Akulkute/MINE-GUARD/Images/WhatsApp Image 2026-06-03 at 1.49.41 AM.jpeg

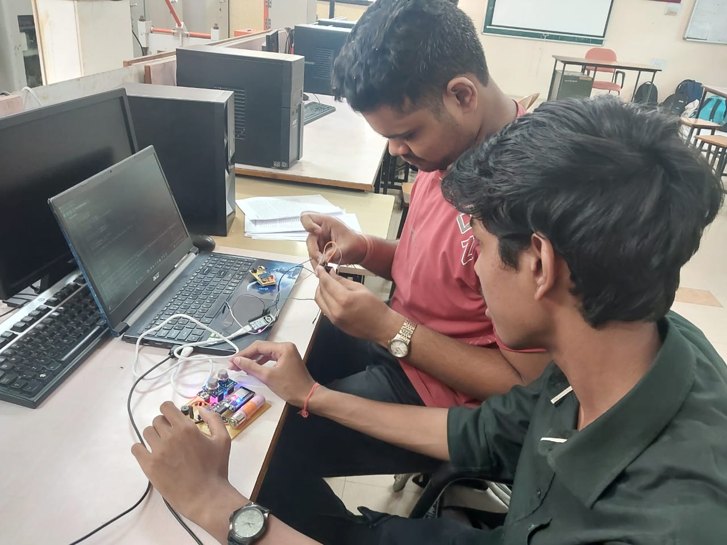
Images/WhatsApp Image 2026-06-03 at 1.49.41 AM.jpeg
