Akulkute/MINE-GUARD/PCB-files/Images/WhatsApp Image 2026-06-03 at 1.44.29 AM.jpeg

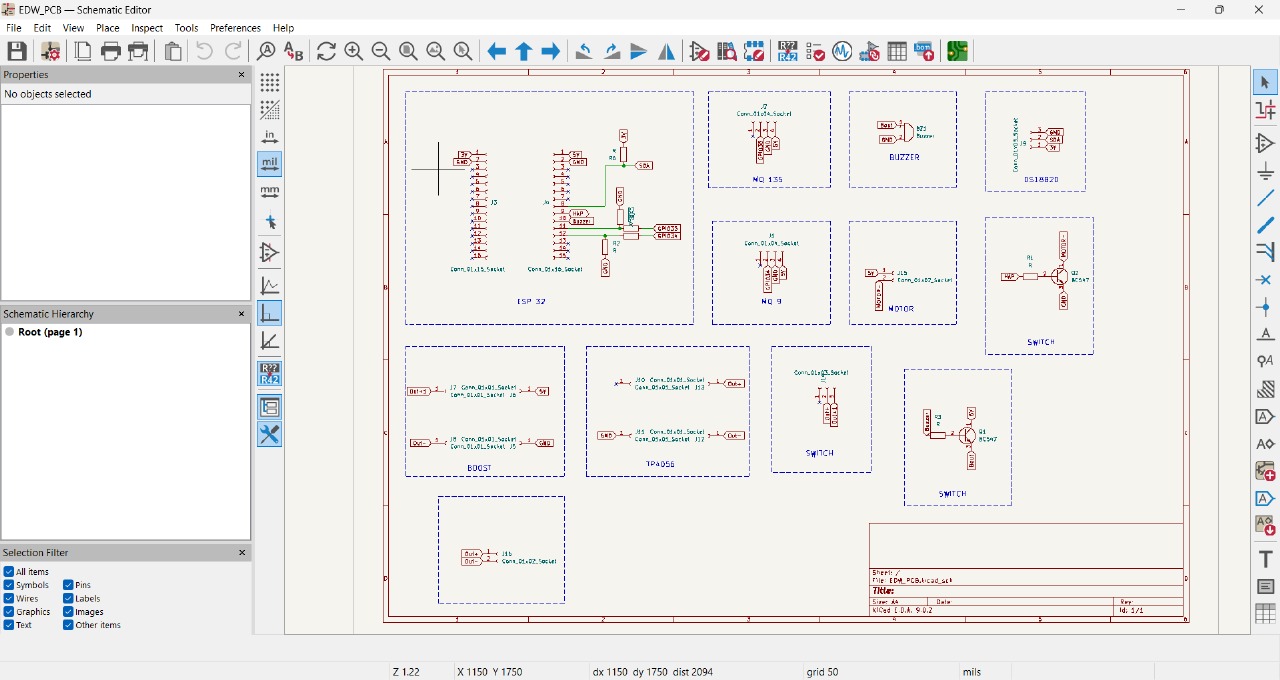
PCB-files/Images/WhatsApp Image 2026-06-03 at 1.44.29 AM.jpeg
